findersee/rctelemetry/hw/Amplifier.asc

C1: cap; 5p
C2: cap; 100n
C3: cap; 10µ
C4: cap; 100n
C5: cap; 10µ
C6: cap; 5p
R1: res; 4.7k
R2: res; 10k
R3: res; 10k
R4: res; 10k
R5: res; 10k
R6: res; 6k2
R7: res; 15k
R8: res; 20k
U1: AD8565
U2: AD8565
V1: voltage; 5
V2: voltage; SINE(3.2 3.2 2k); Rser=15k
V3: voltage; SINE(2.5 2.4 2k)
Named nets: 0, IN, 5V
.tran 10m
.step param R list 0 1k 1.5k 2k 2.5k 3k 3.5k 4k 4.5k 5k 5.5k 6k 6.5k 7k 7.5k 8k 8.5k 9k 9.5k 10k
